madalinaandronache/TSC-Project/Images/OpenBook_CustomView.png

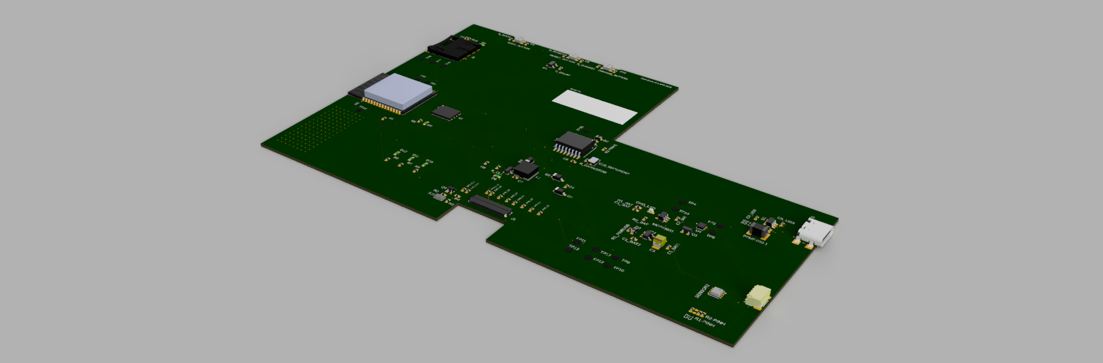
Images/OpenBook_CustomView.png
